eseto2/DIY_Electronic_CNC_Machine/Docs/Diagrams/Motor Support Right.jpg

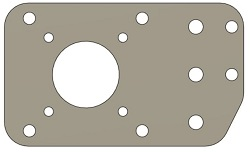
Docs/Diagrams/Motor Support Right.jpg
