eseto2/DIY_Electronic_CNC_Machine/Docs/Diagrams/X Axis.jpg

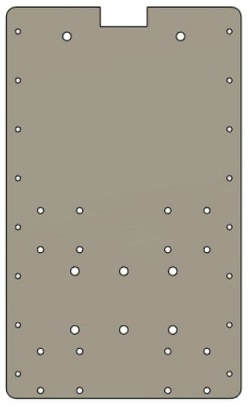
Docs/Diagrams/X Axis.jpg
