eseto2/DIY_Electronic_CNC_Machine/Docs/Diagrams/Y Axis Right.jpg

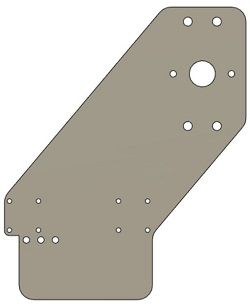
Docs/Diagrams/Y Axis Right.jpg
