eseto2/DIY_Electronic_CNC_Machine/Docs/Diagrams/Z Axis Motor Support.jpg

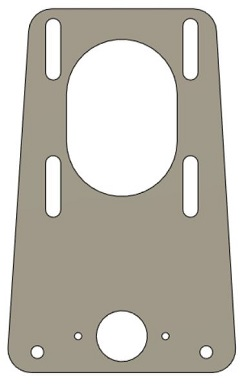
Docs/Diagrams/Z Axis Motor Support.jpg
