eseto2/DIY_Electronic_CNC_Machine/Axis_Carriage/x_axis_carriage_left.stl

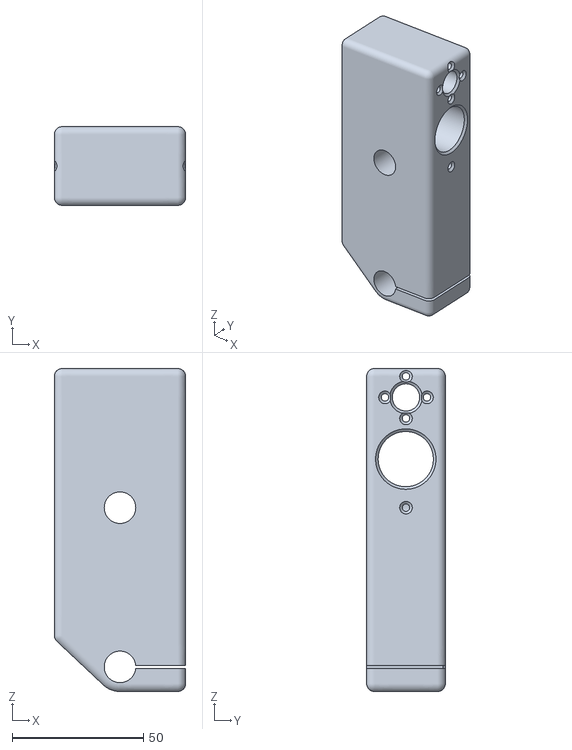
[picture p35: CAD file, 2026-01-09]
Axis_Carriage/x_axis_carriage_left.stl
50.0 x 30.0 x 123.0
