eseto2/DIY_Electronic_CNC_Machine/Electronics_Covers/Impeller_Quiet v2.stl

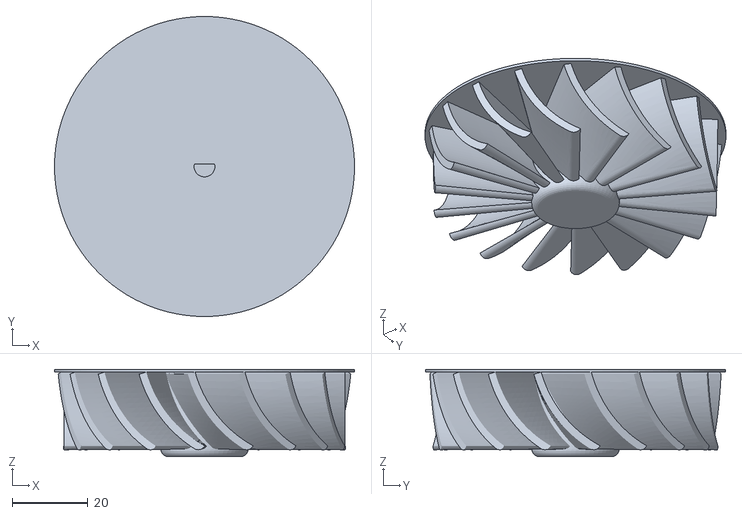
[picture p36: CAD file, 2026-01-09]
Electronics_Covers/Impeller_Quiet v2.stl
79.0 x 79.0 x 23.0
