eseto2/DIY_Electronic_CNC_Machine/Electronics_Covers/Cooler_Fan v1.stl

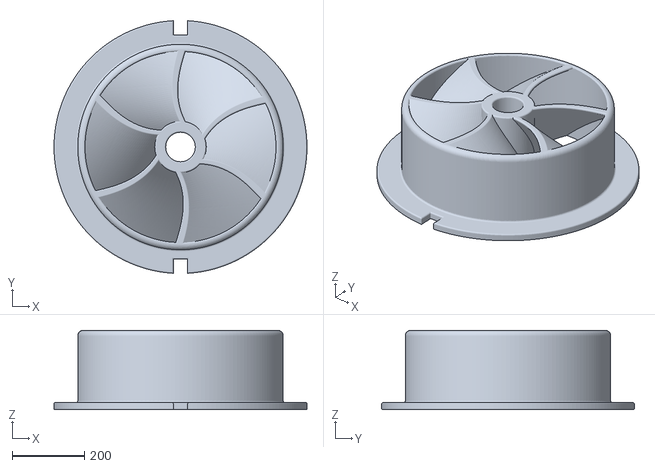
[picture p37: CAD file, 2026-01-09]
Electronics_Covers/Cooler_Fan v1.stl
702.0 x 700.9 x 220.0
