eseto2/DIY_Electronic_CNC_Machine/Electronics_Covers/Impeller v12.stl

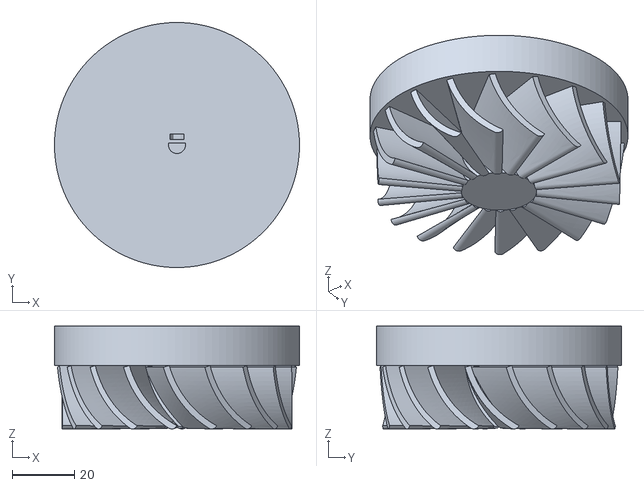
[picture p38: CAD file, 2026-01-09]
Electronics_Covers/Impeller v12.stl
79.0 x 79.0 x 33.2
