eseto2/DIY_Electronic_CNC_Machine/Electronics_Covers/motor_holder v2.stl

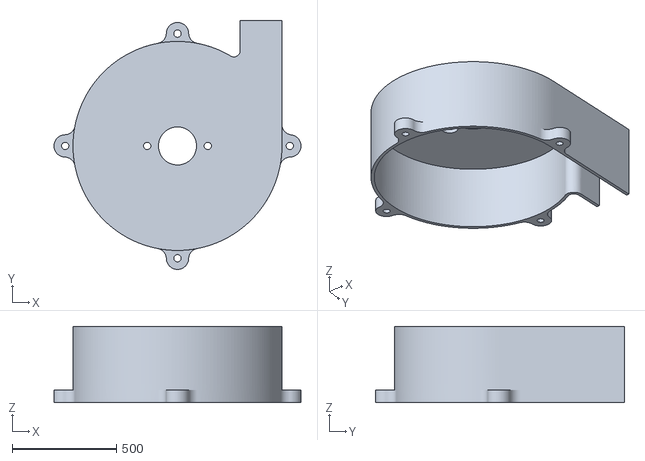
[picture p39: CAD file, 2026-01-09]
Electronics_Covers/motor_holder v2.stl
1182.0 x 1191.0 x 365.0
