eseto2/DIY_Electronic_CNC_Machine/Electronics_Covers/Spindle-HoseMount.stl

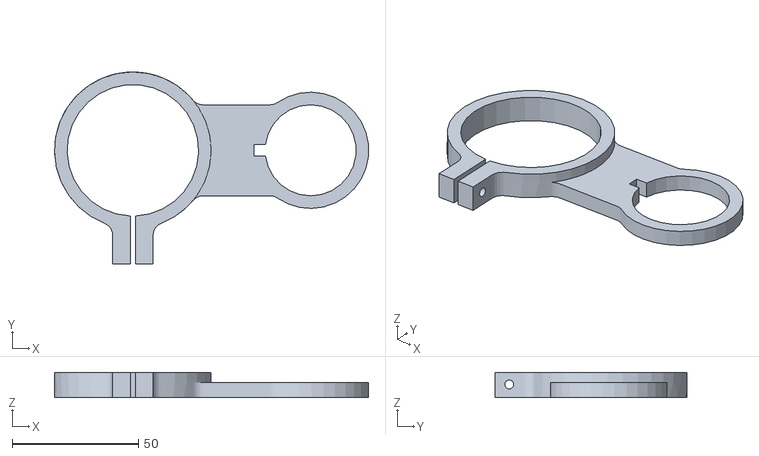
[picture p40: CAD file, 2026-01-09]
Electronics_Covers/Spindle-HoseMount.stl
124.2 x 76.0 x 10.00
