eseto2/DIY_Electronic_CNC_Machine/Electronics_Covers/Dust shoe v8.stl

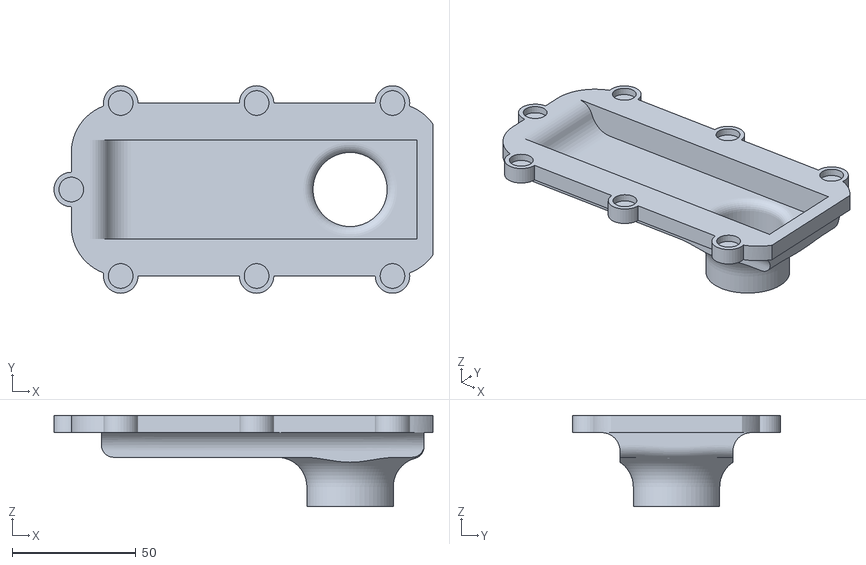
[picture p41: CAD file, 2026-01-09]
Electronics_Covers/Dust shoe v8.stl
153.4 x 84.0 x 37.0
