eseto2/DIY_Electronic_CNC_Machine/Electronics_Covers/DUst COllector Motor mount_normal v2.stl

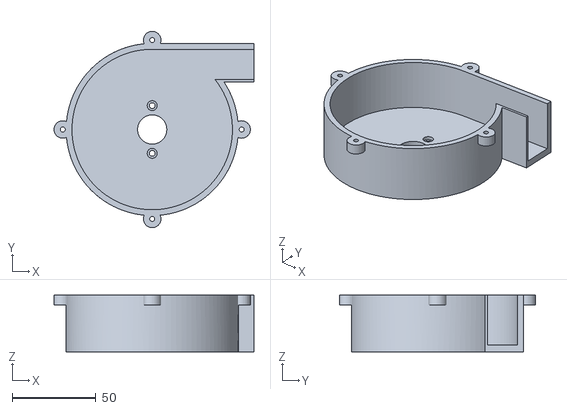
[picture p42: CAD file, 2026-01-09]
Electronics_Covers/DUst COllector Motor mount_normal v2.stl
119.6 x 117.5 x 34.0
