eseto2/DIY_Electronic_CNC_Machine/Electronics_Covers/Motor Mount v17.stl

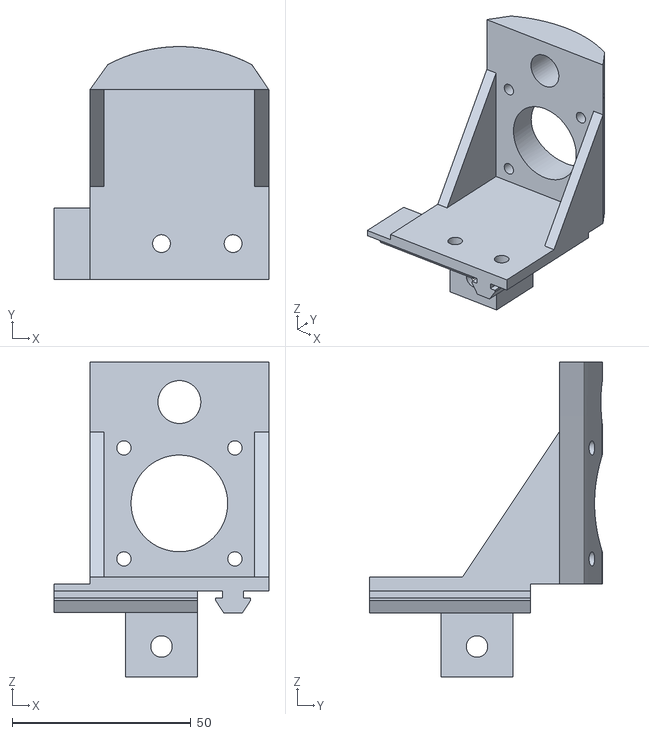
[picture p43: CAD file, 2026-01-09]
Electronics_Covers/Motor Mount v17.stl
60.0 x 65.0 x 88.0
