eseto2/DIY_Electronic_CNC_Machine/Electronics_Covers/gasket.stl

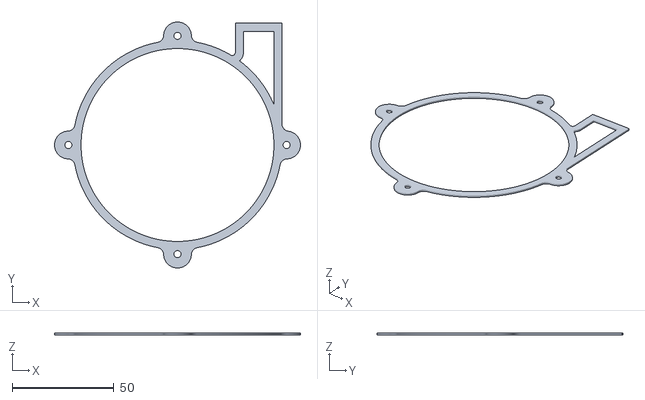
[picture p44: CAD file, 2026-01-09]
Electronics_Covers/gasket.stl
121.2 x 121.2 x 1.00
