eseto2/DIY_Electronic_CNC_Machine/Electronics_Covers/Laser Carriage New v10.stl

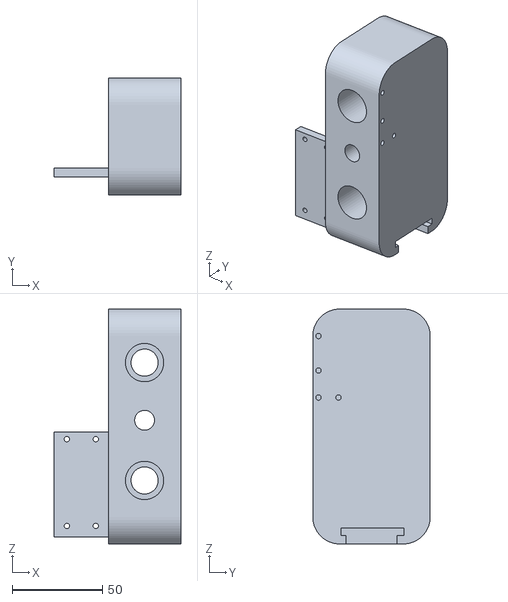
[picture p45: CAD file, 2026-01-09]
Electronics_Covers/Laser Carriage New v10.stl
70.0 x 65.0 x 130.0
